Nosquite/Marcopad-V2.0/pictures/figure2.jpeg

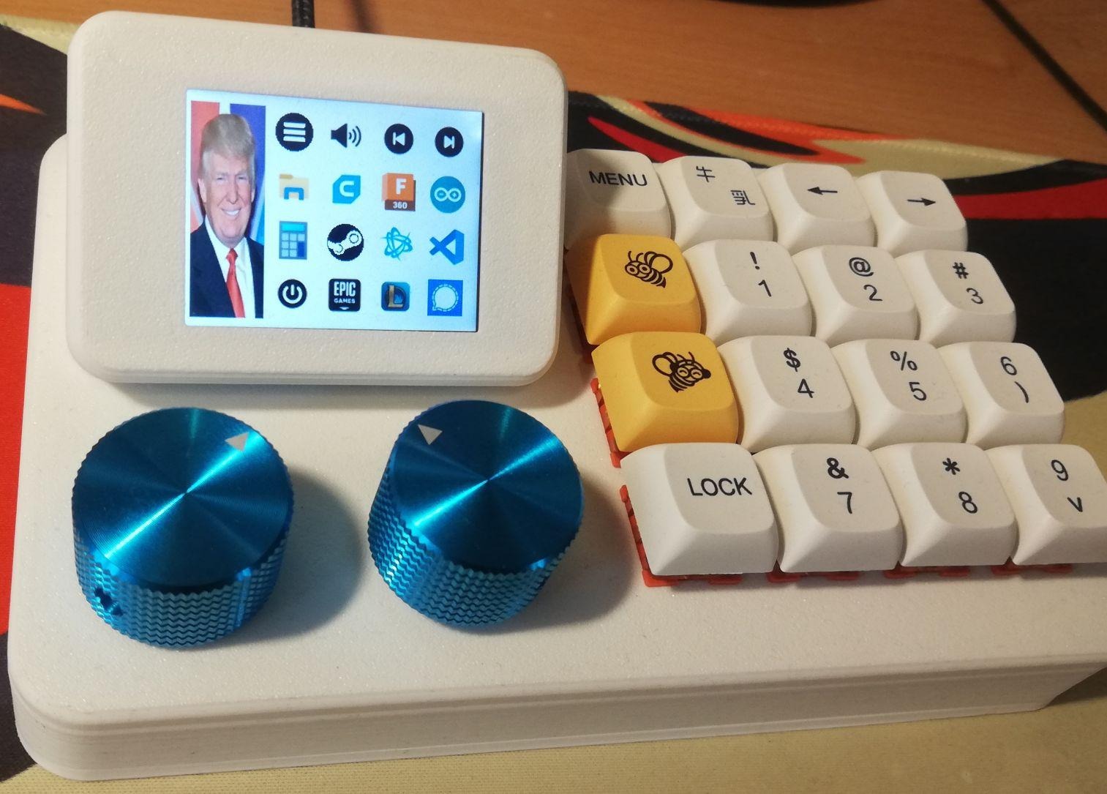
pictures/figure2.jpeg
