Nosquite/Marcopad-V2.0/src/main/pins.h

/*
Display pins
refer to User setup 60 for changes 
DIN -->7
CLK -->6
CS  -->5
DC  -->4
RST -->3
BL  -->none
*/

//encoder 1 pins
#define ENC1_CLK 0
#define ENC1_DT  1
#define ENC1_SW  2

//encoder 2 pins
#define ENC2_CLK 29
#define ENC2_DT  28
#define ENC2_SW  27
